alxgmpr/chipshouter-picoemp/docs/superpowers/plans/2026-07-25-picoemp-rev2026.md

# PicoEMP Rev-2026 Implementation Plan

> **For agentic workers:** REQUIRED SUB-SKILL: Use superpowers:subagent-driven-development (recommended) or superpowers:executing-plans to implement this plan task-by-task. Steps use checkbox (`- [ ]`) syntax for tracking.

**Goal:** Turn the broken in-progress KiCad port into a correct, DRC-clean, 2026-sourceable PicoEMP revision with a hand-buildable DigiKey BOM.

**Architecture:** Copy the existing schematic (whose connectivity is verified correct against the firmware pin map) into a fresh `hardware/rev2026/` project, then repair it in place — symbols, footprints, fields — under a pytest harness that asserts each invariant. Board is re-laid from scratch, replicating the hi-pot-validated HV geometry. Every gate is enforced by `kicad-cli` headlessly.

**Tech Stack:** KiCad 10.0.5 (`kicad-cli` at `/Applications/KiCad/KiCad.app/Contents/MacOS/kicad-cli`), Python 3 via `uv run --with pytest pytest`, the `kicad-happy` plugin skills, git.

**Spec:** `docs/superpowers/specs/2026-07-25-picoemp-rev2026-design.md`

## Tooling — kicad-happy skills

Use these rather than hand-rolling equivalents. Invoke via the Skill tool.

| Skill | Used in | For |
|---|---|---|
| `kicad-happy:bom` | Tasks 2, 3, 12 | `edit_properties.py` to write symbol fields; `bom_manager.py analyze` as a gap gate; `export`/`order` to generate the DigiKey order file |
| `kicad-happy:datasheets` | Tasks 2, 6 | Extract land-pattern and package specs per MPN, cached per project |
| `kicad-happy:lcsc` | Task 2 | Datasheet sync — **the only genuinely no-auth source**. Use this first |
| `kicad-happy:element14` | Task 2 | Datasheet sync — needs a **free** API key (`ELEMENT14_API_KEY`) from partner.element14.com. Simple query-param auth, no OAuth. Best PDF coverage once configured |
| `kicad-happy:digikey` | Task 2, 12 | Part validation and stock. **Requires OAuth setup — see below** |
| `kicad-happy:jlcpcb` | Task 11 | Bare-PCB fab rules and capability limits |
| `kicad-happy:kicad` | Task 13 | Full design review before ordering |

**DigiKey credentials are not configured on this machine** (`DIGIKEY_CLIENT_ID` unset, no `~/.config/secrets.env`). The DigiKey API scripts will fail until the user registers a client-credentials app at developer.digikey.com and exports `DIGIKEY_CLIENT_ID` / `DIGIKEY_CLIENT_SECRET`. **Every DigiKey step below has a no-auth fallback** (element14 or LCSC) so the plan is not blocked on it. Do not stop to ask — use the fallback and note it.

**Known tool limits — verified during execution:**
- `edit_properties.py` **sets and adds** properties; it does not delete them. Field removal uses the Task 1 parser's `property_span()` for a structural rewrite.
- **The datasheet sync scripts do NOT accept `--recursive`.** Valid flags are `--output/-o`, `--force`, `--force-all`, `--delay`, `--parallel`, `--dry-run`, `--json`, and `--mpn-list FILE`. Only `bom_manager.py` and `sync_datasheet_urls.py` take `--recursive`.
- Both sync scripts accept **`--mpn-list FILE`** (one MPN per line). For a design whose schematic MPNs are incomplete, feeding an explicit MPN list is more reliable than parsing the schematic.
- The `jlcpcb` skill does not document minimum routed slot width. Task 11 must check JLCPCB's live capability page.

## Global Constraints

- **Branch:** all work on `rev2026`. Never commit to `main`.
- **Python:** always `uv run --with pytest pytest`. Never raw `pip` or `python -m venv`.
- **Frozen values — never change:** charge PWM 2500 Hz at 1.22% duty; 5 µs default pulse; R3/R7 = 10 Ω; R9 = 2 k; D7 = 18 V ±2%; Pico pin assignment (GP0 trigger, GP6/7/27 LEDs, GP11/GP28 buttons, GP14 HVPULSE, GP18+GP26 CHARGED, GP20 HVPWM).
- **Board:** 2-layer, **1.6 mm thickness**, outline 40 × 116 mm.
- **Designators:** upstream scheme — `D6/D8/D9` LEDs, `P1/P2/P3` headers, `J1` = SMA, `J2` = JST, `J3` = HV tap. New parts: `U2, R14, R15, R16, C6, J4`.
- **Licence:** derivative of CC BY-SA 3.0 work. Attribute NewAE Technology.
- **`kicad-cli` alias:** every command below assumes `KC=/Applications/KiCad/KiCad.app/Contents/MacOS/kicad-cli`.

## ⚠️ Tasks 10 and 11 are human tasks

PCB layout is interactive GUI work. An agent cannot place or route a board. Tasks 10 and 11 must be done by a person in KiCad's PCB editor; the plan supplies the acceptance criteria and the scripted gates that verify the result, not the routing itself. Every other task is fully automatable.

## File Structure

| Path | Responsibility |
|---|---|
| `hardware/rev2026/picoemp-rev2026.kicad_pro` | Project file: netclasses, DRC rules, ERC severities |
| `hardware/rev2026/picoemp-rev2026.kicad_sch` | Schematic (seeded from the kc/ port) |
| `hardware/rev2026/picoemp-rev2026.kicad_pcb` | Board — re-laid from scratch |
| `hardware/rev2026/sym-lib-table` | Project-local symbol libraries |
| `hardware/rev2026/fp-lib-table` | Project-local footprint libraries |
| `hardware/rev2026/lib/picoemp.kicad_sym` | Custom symbols: IGBT-with-diode, LDA111 |
| `hardware/rev2026/lib/picoemp.pretty/` | Custom footprints: ATB322524, LDA111 SOP-6 |
| `hardware/rev2026/tests/kicad_parse.py` | S-expression parser + accessors (shared) |
| `hardware/rev2026/tests/test_schematic.py` | Schematic invariants |
| `hardware/rev2026/tests/test_libraries.py` | Library resolution + custom footprint geometry |
| `hardware/rev2026/tests/test_board.py` | Board setup, netclass, DRC config |
| `hardware/rev2026/tests/conftest.py` | Shared fixtures (paths, parsed docs) |
| `hardware/rev2026/out/` | Generated fab outputs (gitignored) |

`hardware/altium_src/kc/` is left untouched as the as-received reference.

---

### Task 1: Scaffold project and test harness

**Files:**
- Create: `hardware/rev2026/picoemp-rev2026.kicad_sch` (copy)
- Create: `hardware/rev2026/picoemp-rev2026.kicad_pro` (copy)
- Create: `hardware/rev2026/tests/kicad_parse.py`
- Create: `hardware/rev2026/tests/conftest.py`
- Create: `hardware/rev2026/tests/test_schematic.py`

**Interfaces:**
- Consumes: nothing.
- Produces: `kicad_parse.parse_file(path) -> list`, `kicad_parse.symbols(tree) -> list[Symbol]` where `Symbol` is a dataclass with fields `ref: str`, `value: str`, `lib_id: str`, `footprint: str`, `props: dict[str,str]`, `in_bom: bool`, `dnp: bool`. Also `kicad_parse.footprints(tree) -> list[Footprint]` with `ref: str`, `lib_id: str`, `value: str`, `pads: list[tuple[str,float,float]]`. conftest exposes fixtures `sch` (parsed schematic tree) and `syms` (list of Symbol, power symbols excluded).

- [ ] **Step 1: Create the directory and copy the source schematic**

```bash
cd /Users/alex/Downloads/chipshouter-picoemp-main
mkdir -p hardware/rev2026/tests hardware/rev2026/lib/picoemp.pretty hardware/rev2026/out
cp hardware/altium_src/kc/ChipShouter-Pico.kicad_sch hardware/rev2026/picoemp-rev2026.kicad_sch
cp hardware/altium_src/kc/ChipShouter-Pico.kicad_pro hardware/rev2026/picoemp-rev2026.kicad_pro
echo "out/" > hardware/rev2026/.gitignore
```

- [ ] **Step 2: Write the parser**

Create `hardware/rev2026/tests/kicad_parse.py`:

```python
"""Minimal KiCad s-expression parser and accessors for design-rule tests."""
import re
from dataclasses import dataclass, field

def _tokens(s):
    i, n = 0, len(s)
    while i < n:
        c = s[i]
        if c == '"':
            j, buf = i + 1, []
            while j < n:
                if s[j] == '\\':
                    buf.append(s[j + 1]); j += 2; continue
                if s[j] == '"':
                    break
                buf.append(s[j]); j += 1
            yield ('str', ''.join(buf)); i = j + 1
        elif c in '()':
            yield ('paren', c); i += 1
        elif c.isspace():
            i += 1
        else:
            j = i
            while j < n and not s[j].isspace() and s[j] not in '()"':
                j += 1
            yield ('sym', s[i:j]); i = j

def parse(text):
    """Parse s-expression text. Quoted strings become ('S', value) tuples."""
    stack = [[]]
    for kind, val in _tokens(text):
        if kind == 'paren':
            if val == '(':
                stack.append([])
            else:
                node = stack.pop()
                stack[-1].append(node)
        elif kind == 'sym':
            stack[-1].append(val)
        else:
            stack[-1].append(('S', val))
    return stack[0]

def parse_file(path):
    return parse(open(path, encoding='utf-8').read())[0]

def sval(x):
    """Unwrap a quoted-string node, else None."""
    return x[1] if isinstance(x, tuple) and x and x[0] == 'S' else None

def _walk(node, name):
    """Yield every sub-list whose head is `name`, at any depth."""
    if isinstance(node, list):
        if node and node[0] == name:
            yield node
        for child in node:
            yield from _walk(child, name)

@dataclass
class Symbol:
    ref: str = ''
    value: str = ''
    lib_id: str = ''
    footprint: str = ''
    props: dict = field(default_factory=dict)
    in_bom: bool = True
    dnp: bool = False

@dataclass
class Footprint:
    ref: str = ''
    lib_id: str = ''
    value: str = ''
    pads: list = field(default_factory=list)

def symbols(tree, include_power=False):
    out = []
    for node in tree:
        if not (isinstance(node, list) and node and node[0] == 'symbol'):
            continue
        s = Symbol()
        for e in node:
            if not isinstance(e, list) or not e:
                continue
            if e[0] == 'lib_id':
                s.lib_id = sval(e[1]) or ''
            elif e[0] == 'property':
                s.props[sval(e[1])] = sval(e[2])
            elif e[0] == 'in_bom':
                s.in_bom = (e[1] == 'yes')
            elif e[0] == 'dnp':
                s.dnp = (e[1] == 'yes')
        s.ref = s.props.get('Reference', '')
        s.value = s.props.get('Value', '')
        s.footprint = s.props.get('Footprint', '') or ''
        if s.ref.startswith('#') and not include_power:
            continue
        out.append(s)
    return out

def footprints(tree):
    out = []
    for node in _walk(tree, 'footprint'):
        f = Footprint(lib_id=sval(node[1]) or '')
        for e in node:
            if isinstance(e, list) and e and e[0] == 'property':
                if sval(e[1]) == 'Reference':
                    f.ref = sval(e[2]) or ''
                elif sval(e[1]) == 'Value':
                    f.value = sval(e[2]) or ''
        for pad in _walk(node, 'pad'):
            num = sval(pad[1]) or ''
            at = next((c for c in pad if isinstance(c, list) and c and c[0] == 'at'), None)
            if at:
                f.pads.append((num, float(at[1]), float(at[2])))
        out.append(f)
    return out

def ref_key(ref):
    """Sort key: ('R', 9) for 'R9'. Lets R9 sort before R10."""
    m = re.match(r'([A-Za-z]+)(\d+)', ref)
    return (m.group(1), int(m.group(2))) if m else (ref, 0)
```

- [ ] **Step 3: Write conftest fixtures**

Create `hardware/rev2026/tests/conftest.py`:

```python
import pathlib
import sys

import pytest

sys.path.insert(0, str(pathlib.Path(__file__).parent))
import kicad_parse as kp

ROOT = pathlib.Path(__file__).resolve().parents[1]
SCH = ROOT / 'picoemp-rev2026.kicad_sch'
PCB = ROOT / 'picoemp-rev2026.kicad_pcb'
PRO = ROOT / 'picoemp-rev2026.kicad_pro'

@pytest.fixture(scope='session')
def root():
    return ROOT

@pytest.fixture(scope='session')
def sch():
    return kp.parse_file(SCH)

@pytest.fixture(scope='session')
def syms(sch):
    return kp.symbols(sch)
```

- [ ] **Step 4: Write the characterization test**

This asserts the *current* state so we notice unintended drift. Create `hardware/rev2026/tests/test_schematic.py`:

```python
import kicad_parse as kp

# Every non-power reference expected in the design, post-rework.
EXPECTED_REFS = {
    'C1', 'C2', 'C3', 'C5', 'C6',
    'D1', 'D2', 'D3', 'D4', 'D5', 'D6', 'D7', 'D8', 'D9',
    'FID1', 'FID2', 'FID3',
    'J1', 'J2', 'J3', 'J4',
    'MH1', 'MH2', 'MH3',
    'P1', 'P2', 'P3',
    'Q1', 'Q2', 'Q3', 'Q4',
    'R1', 'R2', 'R3', 'R4', 'R5', 'R6', 'R7', 'R9',
    'R10', 'R11', 'R12', 'R13', 'R14', 'R15', 'R16',
    'SW1', 'SW2', 'SW3',
    'T1', 'T2',
    'U1', 'U2',
}

def test_parser_finds_symbols(syms):
    """Sanity: the parser reads a plausible number of components."""
    assert len(syms) > 30

def test_every_symbol_has_a_reference(syms):
    assert all(s.ref for s in syms)

def test_no_duplicate_references(syms):
    refs = [s.ref for s in syms]
    dupes = {r for r in refs if refs.count(r) > 1}
    assert not dupes, f'duplicate refs: {sorted(dupes)}'
```

- [ ] **Step 5: Run the tests — they must pass**

```bash
cd hardware/rev2026 && uv run --with pytest pytest tests/ -v
```

Expected: 3 passed. If `test_no_duplicate_references` fails, stop — the source schematic has a problem the audit did not find.

- [ ] **Step 6: Commit**

```bash
cd /Users/alex/Downloads/chipshouter-picoemp-main
git add hardware/rev2026
git commit -m "Scaffold rev2026 project and pytest design-rule harness"
```

---

### Task 2: Project-local library tables and datasheet sync

**Files:**
- Create: `hardware/rev2026/sym-lib-table`
- Create: `hardware/rev2026/fp-lib-table`
- Create: `hardware/rev2026/lib/picoemp.kicad_sym` (empty shell)
- Create: `hardware/rev2026/tests/test_libraries.py`
- Create: `hardware/datasheets/` (shared across revisions; gitignored)

**Interfaces:**
- Consumes: `kicad_parse` from Task 1.
- Produces: `${KIPRJMOD}/lib/picoemp.kicad_sym` registered as symbol lib `picoemp`; `${KIPRJMOD}/lib/picoemp.pretty` registered as footprint lib `picoemp`. Later tasks reference symbols as `picoemp:<name>` and footprints as `picoemp:<name>`. Also `hardware/datasheets/manifest.json` mapping MPN → local PDF, consumed by Task 6.

- [ ] **Step 1: Write the failing test**

Create `hardware/rev2026/tests/test_libraries.py`:

```python
import kicad_parse as kp

def test_sym_lib_table_exists_and_registers_picoemp(root):
    path = root / 'sym-lib-table'
    assert path.exists(), 'project-local sym-lib-table missing'
    text = path.read_text()
    assert 'picoemp' in text
    assert '${KIPRJMOD}/lib/picoemp.kicad_sym' in text

def test_fp_lib_table_exists_and_registers_picoemp(root):
    path = root / 'fp-lib-table'
    assert path.exists(), 'project-local fp-lib-table missing'
    text = path.read_text()
    assert 'picoemp' in text
    assert '${KIPRJMOD}/lib/picoemp.pretty' in text
```

- [ ] **Step 2: Run to verify it fails**

```bash
cd hardware/rev2026 && uv run --with pytest pytest tests/test_libraries.py -v
```

Expected: 2 failed, "project-local sym-lib-table missing".

- [ ] **Step 3: Create the library tables**

`hardware/rev2026/sym-lib-table`:

```
(sym_lib_table
  (version 7)
  (lib (name "picoemp")(type "KiCad")(uri "${KIPRJMOD}/lib/picoemp.kicad_sym")(options "")(descr "PicoEMP Rev-2026 project symbols"))
)
```

`hardware/rev2026/fp-lib-table`:

```
(fp_lib_table
  (version 7)
  (lib (name "picoemp")(type "KiCad")(uri "${KIPRJMOD}/lib/picoemp.pretty")(options "")(descr "PicoEMP Rev-2026 project footprints"))
)
```

`hardware/rev2026/lib/picoemp.kicad_sym`:

```
(kicad_symbol_lib
  (version 20241209)
  (generator "kicad_symbol_editor")
  (generator_version "10.0")
)
```

- [ ] **Step 4: Run to verify it passes**

```bash
cd hardware/rev2026 && uv run --with pytest pytest tests/test_libraries.py -v
```

Expected: 2 passed.

- [ ] **Step 5: Sync datasheets**

Invoke the `kicad-happy:element14` skill (no auth needed) and run its sync script
against the schematic. Datasheets are essential context for Task 6's footprint
work and for resolving the D7 package question in spec §10.

```bash
SK=/Users/alex/.claude/plugins/cache/kicad-happy/kicad-happy/2.0.0/skills
uv run python $SK/lcsc/scripts/sync_datasheets_lcsc.py \
  hardware/rev2026/picoemp-rev2026.kicad_sch
```

If element14 misses parts, fall back to the `kicad-happy:lcsc` sync — it shares
the same `datasheets/` directory and skips what is already downloaded:

```bash
uv run python $SK/element14/scripts/sync_datasheets_element14.py \
  hardware/rev2026/picoemp-rev2026.kicad_sch   # needs ELEMENT14_API_KEY
```

Do **not** block on DigiKey — its credentials are not configured. If the user
sets them up later, `sync_datasheets_digikey.py` gives the best coverage.

Note the schematic's MPN fields are not normalized until Task 3, so coverage will
be partial here. Re-run this step after Task 3; the scripts are idempotent.

- [ ] **Step 6: Add datasheets to gitignore**

```bash
cd /Users/alex/Downloads/chipshouter-picoemp-main
grep -q '^datasheets/' .gitignore || echo 'datasheets/' >> .gitignore
```

- [ ] **Step 7: Commit**

```bash
git add hardware/rev2026 .gitignore
git commit -m "Add project-local library tables, sync component datasheets"
```

---

### Task 3: Flatten values and normalize BOM fields

Fixes three audit findings at once: `${ALTIUM_VALUE}` indirection, C5's missing value, and the R9 part-number bug.

**Files:**
- Modify: `hardware/rev2026/picoemp-rev2026.kicad_sch`
- Modify: `hardware/rev2026/tests/test_schematic.py`

**Interfaces:**
- Consumes: `Symbol.props` from Task 1.
- Produces: every BOM symbol carries canonical fields `MPN`, `Manufacturer`, `DigiKey`, `Datasheet`. No symbol carries `PART NUMBER`, `ALTIUM_VALUE`, or Altium metadata.

- [ ] **Step 1: Write the failing tests**

Append to `hardware/rev2026/tests/test_schematic.py`:

```python
ALTIUM_CRUFT = {
    'PART NUMBER', 'ALTIUM_VALUE', 'COMPONENT GROUP', 'COMPONENT KIND',
    'COMPONENT TYPE', 'PIN COUNT', 'PP MATERIAL STACK', 'PP ROTATION',
    'PP ROTATION1', 'MOUNTING TECHNOLOGY', 'LATESTREVISIONDATE',
    'LATESTREVISIONNOTE', 'PUBLISHER', 'SNAPEDA_LINK', 'CHECK_PRICES',
    'AVAILABILITY', 'PRICE', 'MANUFACTURE 1', 'MANUFACTURE PART NUMBER 1',
    'SUPPLIER 1', 'SUPPLIER PART NUMBER 1', 'MANUFACTURER_NAME',
    'MANUFACTURER_PART_NUMBER', 'MOUSER PART NUMBER', 'MOUSER PRICE/STOCK',
    'ARROW PART NUMBER', 'ARROW PRICE/STOCK', 'DATASHEET LINK', 'ROHS',
    'CASE-EIA', 'CASE-METRIC', 'RATED POWER', 'RATED VOLTAGE', 'TOLERANCE',
    'TEMPERATURE RANGE', 'HEIGHT', 'PACKAGE', 'PURCHASE-URL', 'MP', 'MF',
}

def test_no_unresolved_value_variables(syms):
    bad = [s.ref for s in syms if '${' in s.value]
    assert not bad, f'symbols with unresolved value variables: {bad}'

def test_c5_has_its_value(syms):
    c5 = next(s for s in syms if s.ref == 'C5')
    assert c5.value == '100n'

def test_no_altium_cruft_fields(syms):
    offenders = {s.ref: sorted(set(s.props) & ALTIUM_CRUFT)
                 for s in syms if set(s.props) & ALTIUM_CRUFT}
    assert not offenders, f'Altium metadata remains: {offenders}'

def test_r9_part_data_is_2k_not_75r():
    """Upstream bug: R9 carried R4's part data throughout."""
    import conftest
    syms = kp.symbols(kp.parse_file(conftest.SCH))
    r9 = next(s for s in syms if s.ref == 'R9')
    assert r9.value == '2k'
    assert r9.props.get('MPN') == 'RC0805FR-072KL'
    assert r9.props.get('DigiKey') == '311-2.00KCRCT-ND'
```

- [ ] **Step 2: Run to verify they fail**

```bash
cd hardware/rev2026 && uv run --with pytest pytest tests/test_schematic.py -v
```

Expected: 4 failed — unresolved `${ALTIUM_VALUE}` on 11 symbols, C5 value wrong, cruft present, R9 has no `MPN`.

- [ ] **Step 3: Write the field-rewrite script**

Create `hardware/rev2026/tools/normalize_fields.py`:

```python
"""One-shot: flatten ${ALTIUM_VALUE}, rename fields to canonical names,
strip Altium metadata. Operates on the schematic text directly to preserve
formatting and UUIDs."""
import pathlib
import re
import sys

sys.path.insert(0, str(pathlib.Path(__file__).resolve().parents[1] / 'tests'))
import kicad_parse as kp

SCH = pathlib.Path(__file__).resolve().parents[1] / 'picoemp-rev2026.kicad_sch'

RENAME = {
    'MANUFACTURE PART NUMBER 1': 'MPN',
    'MANUFACTURER_PART_NUMBER': 'MPN',
    'MANUFACTURE 1': 'Manufacturer',
    'MANUFACTURER_NAME': 'Manufacturer',
    'SUPPLIER PART NUMBER 1': 'DigiKey',
}

DROP = {
    'PART NUMBER', 'COMPONENT GROUP', 'COMPONENT KIND', 'COMPONENT TYPE',
    'PIN COUNT', 'PP MATERIAL STACK', 'PP ROTATION', 'PP ROTATION1',
    'MOUNTING TECHNOLOGY', 'LATESTREVISIONDATE', 'LATESTREVISIONNOTE',
    'PUBLISHER', 'SNAPEDA_LINK', 'CHECK_PRICES', 'AVAILABILITY', 'PRICE',
    'SUPPLIER 1', 'MOUSER PART NUMBER', 'MOUSER PRICE/STOCK',
    'ARROW PART NUMBER', 'ARROW PRICE/STOCK', 'ROHS', 'CASE-EIA',
    'CASE-METRIC', 'RATED POWER', 'RATED VOLTAGE', 'TOLERANCE',
    'TEMPERATURE RANGE', 'HEIGHT', 'PACKAGE', 'PURCHASE-URL', 'MP', 'MF',
    'DATASHEET LINK',
}

def main():
    text = SCH.read_text(encoding='utf-8')

    # 1. Flatten ${ALTIUM_VALUE} using each symbol's own ALTIUM_VALUE property.
    #    Symbol blocks start at a tab-tab (lib_id line; split on those boundaries.
    starts = [m.start() for m in re.finditer(r'\n\t\t\(lib_id "', text)]
    starts.append(len(text))
    out = [text[:starts[0]]] if starts else [text]
    for a, b in zip(starts, starts[1:]):
        blk = text[a:b]
        av = re.search(r'\(property "ALTIUM_VALUE"\s+"([^"]*)"', blk)
        if av and '${ALTIUM_VALUE}' in blk:
            blk = blk.replace('${ALTIUM_VALUE}', av.group(1))
        out.append(blk)
    text = ''.join(out)

    # 2. Rename fields.
    for old, new in RENAME.items():
        text = text.replace(f'(property "{old}"', f'(property "{new}"')

    # 3. Drop unwanted property blocks (single-level, tab-tab-tab indented).
    for name in DROP | {'ALTIUM_VALUE'}:
        pattern = re.compile(
            r'\n\t\t\t\(property "' + re.escape(name) + r'"(?:[^()]|\((?:[^()]|\([^()]*\))*\))*\)',
            re.S)
        text = pattern.sub('', text)

    SCH.write_text(text, encoding='utf-8')
    print('normalized')

if __name__ == '__main__':
    main()
```

- [ ] **Step 4: Run the deletion/flatten script**

This handles only flattening, renaming and removal — `edit_properties.py` cannot
delete properties.

```bash
cd hardware/rev2026 && uv run python tools/normalize_fields.py
```

- [ ] **Step 5: Set the corrected values with the bom skill**

Invoke `kicad-happy:bom`, then use its `edit_properties.py` rather than clicking
through the GUI. KiCad must be closed, or the changes will be overwritten by its
in-memory copy.

```bash
SK=/Users/alex/.claude/plugins/cache/kicad-happy/kicad-happy/2.0.0/skills
cd /Users/alex/Downloads/chipshouter-picoemp-main
cat > /tmp/updates.json <<'EOF'
{
  "C5": {"Value": "100n", "MPN": "C0603C104K5RACTU", "Manufacturer": "KEMET",
         "DigiKey": "399-5089-2-ND"},
  "R9": {"Value": "2k", "MPN": "RC0805FR-072KL", "Manufacturer": "Yageo",
         "DigiKey": "311-2.00KCRCT-ND"}
}
EOF
uv run python $SK/bom/scripts/edit_properties.py \
  hardware/rev2026/picoemp-rev2026.kicad_sch --updates /tmp/updates.json --dry-run
```

Review the dry-run diff, then re-run without `--dry-run`.

- [ ] **Step 6: Backfill the remaining MPN and DigiKey fields**

Build the rest of `/tmp/updates.json` from spec §5.2 and §5.3 and apply it the same
way. Every BOM symbol needs `MPN`, `Manufacturer` and `DigiKey`. Use the DigiKey
part numbers already recorded in the spec — they came from upstream's published
BOM and were verified Active during the audit.

- [ ] **Step 7: Gate on the bom skill's gap report**

```bash
uv run python $SK/bom/scripts/bom_manager.py analyze \
  hardware/rev2026/picoemp-rev2026.kicad_sch --json --recursive \
  | python3 -c "import json,sys; d=json.load(sys.stdin); \
print('without_mpn:', d['stats']['without_mpn']); \
print(json.dumps(d['convention']['field_mapping'], indent=1))"
```

Expected: `without_mpn: 0`, and the field mapping resolves `mpn` → `MPN`,
`manufacturer` → `Manufacturer`. If the analyzer still reports `PART NUMBER` as
the MPN field, the deletion step did not take.

- [ ] **Step 8: Run tests to verify they pass**

```bash
cd hardware/rev2026 && uv run --with pytest pytest tests/test_schematic.py -v
```

Expected: all passed.

- [ ] **Step 9: Re-run the datasheet sync**

Now that MPNs are populated, coverage will be much better. Idempotent.

```bash
uv run python $SK/lcsc/scripts/sync_datasheets_lcsc.py \
  hardware/rev2026/picoemp-rev2026.kicad_sch
uv run python $SK/bom/scripts/sync_datasheet_urls.py \
  hardware/rev2026/picoemp-rev2026.kicad_sch --recursive --dry-run
```

Review, then re-run the URL backfill without `--dry-run` to populate empty
`Datasheet` fields from the manifest.

- [ ] **Step 10: Commit**

```bash
git add hardware/rev2026
git commit -m "Flatten Altium value variables, normalize BOM fields, fix R9 part data

R9's value is 2k but every part field carried R4's 75R data
(RCHIP-75R-0805 / RC0805FR-0775RL / 311-75.0CRCT-ND). This is an
upstream defect in the Altium source; the published .xls BOM has the
correct RC0805FR-072KL. design_notes confirms 2k is the validated
gate-drive shunt."
```

---

### Task 4: Custom symbols — IGBT with antiparallel diode, LDA111

**Files:**
- Modify: `hardware/rev2026/lib/picoemp.kicad_sym`
- Modify: `hardware/rev2026/tests/test_libraries.py`

**Interfaces:**
- Consumes: `picoemp` symbol lib from Task 2.
- Produces: symbols `picoemp:IGBT_NCH_Diode` (3 pins: 1=G, 2=C, 3=E) and `picoemp:LDA111` (6 pins: 1=A, 2=K, 4=E, 5=C, 6=B; pin 3 absent). Task 5 assigns these.

- [ ] **Step 1: Write the failing test**

Append to `hardware/rev2026/tests/test_libraries.py`:

```python
def _lib_symbol_names(root):
    text = (root / 'lib' / 'picoemp.kicad_sym').read_text()
    return set(re.findall(r'\n\t\(symbol "([^"]+)"', text))

def test_custom_symbols_exist(root):
    names = _lib_symbol_names(root)
    assert 'IGBT_NCH_Diode' in names, 'IGBT symbol with antiparallel diode missing'
    assert 'LDA111' in names, 'LDA111 Darlington opto symbol missing'

def test_igbt_pin_names(root):
    """DPAK IGBT: pin 1 Gate, pin 2 Collector, pin 3 Emitter."""
    text = (root / 'lib' / 'picoemp.kicad_sym').read_text()
    body = text.split('(symbol "IGBT_NCH_Diode"')[1].split('\n\t(symbol "')[0]
    for num, name in (('1', 'G'), ('2', 'C'), ('3', 'E')):
        assert f'(name "{name}"' in body, f'IGBT missing pin name {name}'
        assert f'(number "{num}"' in body, f'IGBT missing pin number {num}'

def test_lda111_pin_numbers(root):
    """6-pin opto, pin 3 is absent (NC)."""
    text = (root / 'lib' / 'picoemp.kicad_sym').read_text()
    body = text.split('(symbol "LDA111"')[1].split('\n\t(symbol "')[0]
    nums = set(re.findall(r'\(number "(\d)"', body))
    assert nums == {'1', '2', '4', '5', '6'}, f'unexpected LDA111 pins: {sorted(nums)}'
```

Add `import re` at the top of the file.

- [ ] **Step 2: Run to verify it fails**

```bash
cd hardware/rev2026 && uv run --with pytest pytest tests/test_libraries.py -v
```

Expected: 3 failed, "IGBT symbol with antiparallel diode missing".

- [ ] **Step 3: Author the two symbols**

Either draw them in KiCad's Symbol Editor, or author the `.kicad_sym`
s-expressions directly — the file format is plain text and the tests below
validate structure either way. Authoring directly is usually faster and is
fully scriptable.

Whichever route, both symbols must pass the validation in Step 3b.

**`IGBT_NCH_Diode`** — start from `Device:Q_NIGBT_GCE`, then add a diode from collector to emitter (cathode at collector) to represent the co-packed antiparallel diode. Pins: `1` = `G` (input), `2` = `C` (passive), `3` = `E` (passive). Set `Value` = `RGT16BM65DTL`, `Footprint` = `Package_TO_SOT_SMD:TO-252-3_TabPin2`, `Datasheet` = `https://fscdn.rohm.com/en/products/databook/datasheet/discrete/igbt/rgt16bm65d-e.pdf`.

**`LDA111`** — an LED (pins 1 anode / 2 cathode) optically coupled to a Darlington pair with the base brought out. Pins: `1` = `A`, `2` = `K`, `4` = `E`, `5` = `C`, `6` = `B`. **No pin 3** — it is a no-connect on the physical part. Set `Value` = `LDA111STR`, `Footprint` = `picoemp:SOP-6_LDA111`, `Datasheet` = `https://www.littelfuse.com/products/power-semiconductors-control-ics/integrated-circuits/optocouplers/single-optocouplers/lda111`.

- [ ] **Step 3b: Validate that KiCad can actually load and render both symbols**

Structural tests prove the pins are right; these prove KiCad accepts the file.

```bash
KC=/Applications/KiCad/KiCad.app/Contents/MacOS/kicad-cli
cd /Users/alex/Downloads/chipshouter-picoemp-main/hardware/rev2026

# Parse gate: non-zero exit or an error means the library is malformed.
"$KC" sym upgrade --force -o /tmp/picoemp-upgraded.kicad_sym lib/picoemp.kicad_sym

# Render gate: KiCad must be able to draw both symbols.
mkdir -p /tmp/symsvg && "$KC" sym export svg -o /tmp/symsvg lib/picoemp.kicad_sym
ls /tmp/symsvg
```

Expected: `sym upgrade` exits 0, and `/tmp/symsvg` contains an SVG per symbol.
An empty output directory means KiCad silently rejected the symbol — treat that
as a failure even if `sym upgrade` passed.

- [ ] **Step 4: Run to verify it passes**

```bash
cd hardware/rev2026 && uv run --with pytest pytest tests/test_libraries.py -v
```

Expected: all passed.

- [ ] **Step 5: Commit**

```bash
git add hardware/rev2026/lib hardware/rev2026/tests
git commit -m "Add custom symbols: IGBT with antiparallel diode, LDA111 Darlington opto"
```

---

### Task 5: Correct all symbol assignments

**Files:**
- Modify: `hardware/rev2026/picoemp-rev2026.kicad_sch`
- Modify: `hardware/rev2026/tests/test_schematic.py`

**Interfaces:**
- Consumes: `picoemp:IGBT_NCH_Diode`, `picoemp:LDA111` from Task 4.
- Produces: no symbol uses a depletion-MOSFET, Schottky, or unresolvable `lib_id`.

- [ ] **Step 1: Write the failing tests**

Append to `hardware/rev2026/tests/test_schematic.py`:

```python
def test_no_wildcard_or_altium_lib_ids(syms):
    bad = [(s.ref, s.lib_id) for s in syms
           if '*' in s.lib_id or 'AltiumLib' in s.lib_id or 'DBLib' in s.lib_id]
    assert not bad, f'unresolvable lib_ids: {bad}'

def test_mosfets_are_enhancement_not_depletion(syms):
    bad = [s.ref for s in syms if 'Depletion' in s.lib_id]
    assert not bad, f'depletion-mode symbol used for enhancement parts: {bad}'

def test_igbt_uses_igbt_symbol(syms):
    q2 = next(s for s in syms if s.ref == 'Q2')
    assert q2.lib_id == 'picoemp:IGBT_NCH_Diode'

def test_rectifiers_are_not_schottky(syms):
    """Upstream errata: D1/D3/D4/D5 were never Schottky diodes."""
    for ref in ('D1', 'D3', 'D4', 'D5'):
        s = next(x for x in syms if x.ref == ref)
        assert 'Schottky' not in s.lib_id, f'{ref} still drawn as Schottky'

def test_opto_uses_custom_symbol(syms):
    q1 = next(s for s in syms if s.ref == 'Q1')
    assert q1.lib_id == 'picoemp:LDA111'

def test_transformers_use_project_symbol(syms):
    for ref in ('T1', 'T2'):
        s = next(x for x in syms if x.ref == ref)
        assert s.lib_id == 'picoemp:ATB322524'

def test_mosfets_use_numeric_pin_symbol(syms):
    """SOT-23 pads are 1/2/3, so the symbol's pins must be too."""
    for ref in ('Q3', 'Q4'):
        s = next(x for x in syms if x.ref == ref)
        assert s.lib_id == 'Transistor_FET:Q_NMOS_GSD'
```

- [ ] **Step 2: Run to verify they fail**

```bash
cd hardware/rev2026 && uv run --with pytest pytest tests/test_schematic.py -v
```

Expected: 6 failed.

- [ ] **Step 3: Create the `picoemp:ATB322524` transformer symbol**

`Device:Transformer_1P_1S` groups pins 1,2 as primary and 3,4 as secondary.
**This design is wired primary = 1,4 and secondary = 2,3** — verified from the
netlist: T1 pin 1 → Q3 drain, pin 4 → C1 (primary); pin 2 → D2 anode, pin 3 →
D7 anode (secondary). T2 follows the same grouping.

Add `ATB322524` to `lib/picoemp.kicad_sym`: two windings, primary on pins 1 and
4, secondary on pins 2 and 3, all `passive`. `Reference` prefix `T`, `Value`
`ATB322524-0110-T000`. Place the polarity dot to match the existing Altium
symbol's graphics and `hardware/BUILD-DRAWING-REV04.PDF` — upstream flags
transformer orientation as a build hazard, and reversing it produced the
wrong-polarity spike on the original prototype.

Validate with the same gates Task 4 used: `kicad-cli sym upgrade --force` must
exit 0 and `sym export svg` must render it.

- [ ] **Step 4: Swap the symbols**

| Ref | New `lib_id` | Pin numbers change? |
|---|---|---|
| Q2 | `picoemp:IGBT_NCH_Diode` | **yes** — `D`,`G`,`S` → `1`,`2`,`3` |
| Q3, Q4 | `Transistor_FET:Q_NMOS_GSD` | **yes** — `D`,`G`,`S` → `1`,`2`,`3` |
| D1, D3, D4, D5 | `Device:D_Small` | no |
| Q1 | `picoemp:LDA111` | no (pin 3 dropped, was unconnected) |
| T1, T2 | `picoemp:ATB322524` | no |

**⚠️ Q2, Q3 and Q4 change pin numbering, so KiCad cannot auto-preserve their
connections.** It matches by pin number, and `D` does not map to `2`. Reconnect
these deliberately to exactly this mapping:

| Ref | Old pin | Net | New pin |
|---|---|---|---|
| Q2 | `G` | `Net-(D7-K)` | `1` (G) |
| Q2 | `D` | `Net-(J6-Ext)` | `2` (C) |
| Q2 | `S` | `Net-(D7-A)` | `3` (E) |
| Q3 | `G` | `Net-(D4-K)` | `1` (G) |
| Q3 | `S` | `GND` | `2` (S) |
| Q3 | `D` | `Net-(Q3-PadD)` | `3` (D) |
| Q4 | `G` | `Net-(D5-K)` | `1` (G) |
| Q4 | `S` | `GND` | `2` (S) |
| Q4 | `D` | `Net-(Q4-PadD)` | `3` (D) |

Getting this wrong swaps gate and collector on a 650 V IGBT. Match on the
*connection*, not the literal net-name string, in case names have drifted.

- [ ] **Step 4b: Verify the remap**

Export the netlist and confirm each transistor's pin→net mapping matches the
table above. Every other component's connectivity must be byte-identical to
before this task.

- [ ] **Step 4: Run to verify they pass**

```bash
cd hardware/rev2026 && uv run --with pytest pytest tests/test_schematic.py -v
```

Expected: all passed.

- [ ] **Step 5: Commit**

```bash
git add hardware/rev2026
git commit -m "Correct symbol classes: IGBT, enhancement MOSFETs, non-Schottky rectifiers

D1/D3/D4/D5 were drawn as Schottky diodes. This is a documented
upstream errata - hardware/README.md notes the schematic 'claimed they
were Schottky diodes, but as @settinger caught this was never the case'."
```

---

### Task 6: Custom footprints — ATB322524 and LDA111

**Files:**
- Create: `hardware/rev2026/lib/picoemp.pretty/ATB322524.kicad_mod`
- Create: `hardware/rev2026/lib/picoemp.pretty/SOP-6_LDA111.kicad_mod`
- Modify: `hardware/rev2026/tests/test_libraries.py`

**Interfaces:**
- Consumes: `picoemp` footprint lib from Task 2.
- Produces: footprints `picoemp:ATB322524` (4 pads) and `picoemp:SOP-6_LDA111` (5 pads, numbered 1,2,4,5,6). Task 7 assigns these.

- [ ] **Step 1: Write the failing test**

Append to `hardware/rev2026/tests/test_libraries.py`:

```python
import kicad_parse as kp

def _fp(root, name):
    return kp.footprints(kp.parse_file(root / 'lib' / 'picoemp.pretty' / f'{name}.kicad_mod'))[0]

def test_atb322524_footprint_geometry(root):
    """TDK ATB3225: 3.2 x 2.5 mm body, 4 pads, two per side."""
    fp = _fp(root, 'ATB322524')
    assert len(fp.pads) == 4, f'expected 4 pads, got {len(fp.pads)}'
    xs = sorted({round(x, 2) for _, x, _ in fp.pads})
    assert len(xs) == 2, f'pads should form two columns, got x positions {xs}'
    assert 2.0 <= (xs[1] - xs[0]) <= 3.2, f'pad column spacing {xs[1]-xs[0]} mm out of range'

def test_lda111_footprint_has_all_six_pads(root):
    """Pin 3 is electrically NC but the lead physically exists, so it needs a
    pad. Verified against the original SamacSys footprint in
    hardware/altium_src/kc/ChipShouter-Pico.kicad_pcb, which has 6 pads with
    pad 3 at (-4.425, 2.54). Omitting it would leave a lead unsoldered."""
    fp = _fp(root, 'SOP-6_LDA111')
    nums = {n for n, _, _ in fp.pads}
    assert nums == {'1', '2', '3', '4', '5', '6'}, f'unexpected pads: {sorted(nums)}'

def test_lda111_footprint_geometry(root):
    """SOP254P952X470-6N: 2.54 mm pitch, pad centres at x = +/-4.425
    (8.85 mm span). The 9.52 mm in the package name is lead-tip to lead-tip,
    not pad centre to pad centre."""
    fp = _fp(root, 'SOP-6_LDA111')
    ys = sorted({round(y, 2) for _, _, y in fp.pads})
    pitches = {round(b - a, 2) for a, b in zip(ys, ys[1:])}
    assert pitches == {2.54}, f'expected uniform 2.54 mm pitch, got y positions {ys}'
    xs = sorted({round(x, 2) for _, x, _ in fp.pads})
    assert len(xs) == 2, f'pads should form two rows, got x positions {xs}'
    span = xs[1] - xs[0]
    assert 8.6 <= span <= 9.1, f'pad-centre span {span} mm, expected ~8.85'
```

- [ ] **Step 2: Run to verify it fails**

```bash
cd hardware/rev2026 && uv run --with pytest pytest tests/test_libraries.py -v
```

Expected: 3 failed with `FileNotFoundError`.

- [ ] **Step 3: Extract the land patterns from the datasheets**

Invoke the `kicad-happy:datasheets` skill and extract structured package specs for
`ATB322524-0110-T000` and `LDA111STR` from the PDFs synced in Task 2. Work from
those numbers, not from memory or distributor parametrics — the audit found
distributor data wrong on package for both D7 and the SM4005PL.

If a PDF is missing from `hardware/datasheets/`, fetch the TDK ATB3225 datasheet
from `https://mm.digikey.com/Volume0/opasdata/d220001/medias/docus/644/ATB322515-(15,24)_DS.pdf`.

Record for each: body dimensions, pad size, pad pitch, row span, and the
manufacturer's recommended land pattern.

- [ ] **Step 4: Draw the footprints**

Open KiCad → Footprint Editor → `picoemp` library.

**`ATB322524`** — body 3.2 × 2.5 mm max, height 2.4 mm max. Four terminals: pins 1 and 4 on one side, 2 and 3 on the other. Use the datasheet's recommended land pattern. Add a **polarity dot marker on the silkscreen at pin 1** — upstream flags transformer orientation as a build hazard, and reversing it produced the wrong-polarity spike on the original prototype.

**`SOP-6_LDA111`** — 6-pin gull-wing, 2.54 mm pitch (SamacSys name
`SOP254P952X470-6N`, body height 4.70 mm). **Include all six pads.** Pin 3 is
electrically NC but its lead physically exists — the original SamacSys footprint
has 6 pads with pad 3 at (−4.425, 2.54), and omitting it would leave a lead
unsoldered. Pad centres sit at x = ±4.425 (8.85 mm span); the 9.52 mm in the
package name is lead-tip to lead-tip, not pad centre to pad centre.

Mark pin 1 on the silkscreen; upstream's build notes call this out specifically
as easy to get wrong.

⚠️ **Parity note for Task 11.** The `picoemp:LDA111` symbol has five pins (no
pin 3), while this footprint has six pads. Pad 3 will carry no net. If Task 11's
`pcb drc --schematic-parity` flags the unmatched pad, the fix is to restore
pin 3 to the symbol as an `unconnected`-type pin and place a no-connect flag on
it in the schematic — which is what the original Altium design did. Do not
delete the pad.

- [ ] **Step 5: Verify D7 and the rectifier lands against their datasheets**

Two spec §10 items resolve here. Using the extracted specs, confirm:

- **D7 `MM3Z18VB` is SOD-323F** (flat lead, 200 mW), not plain SOD-323. If the
  datasheet says otherwise, change the Task 7 footprint map accordingly.
- **`SM4005PL-TP` is SOD-123FL** with a ~2.36 mm land span, and KiCad's
  `Diode_SMD:D_SOD-123F` matches it within tolerance. If it does not, draw a
  `picoemp:D_SOD-123FL` and use that instead.

Record the outcome in the commit message.

- [ ] **Step 6: Run to verify it passes**

```bash
cd hardware/rev2026 && uv run --with pytest pytest tests/test_libraries.py -v
```

Expected: all passed. If the pitch assertion fails, re-measure against the datasheet rather than loosening the test.

- [ ] **Step 7: Commit**

```bash
git add hardware/rev2026/lib hardware/rev2026/tests
git commit -m "Add ATB322524 transformer and LDA111 SOP-6 footprints with pin-1 markers

Land patterns extracted from manufacturer datasheets rather than
distributor parametrics - the audit found distributor package data
wrong for both D7 (SOD-323 vs SOD-323F) and SM4005PL-TP."
```

---

### Task 7: Assign every footprint

**Files:**
- Modify: `hardware/rev2026/picoemp-rev2026.kicad_sch`
- Modify: `hardware/rev2026/tests/test_schematic.py`

**Interfaces:**
- Consumes: custom footprints from Task 6, library tables from Task 2.
- Produces: every BOM symbol has a `Lib:Name` footprint that resolves.

- [ ] **Step 1: Write the failing tests**

Append to `hardware/rev2026/tests/test_schematic.py`:

```python
FOOTPRINTS = {
    'C1': 'Capacitor_SMD:C_0805_2012Metric',
    'C2': 'Capacitor_SMD:C_0805_2012Metric',
    'C3': 'Capacitor_SMD:C_2220_5750Metric',
    'C5': 'Capacitor_SMD:C_0603_1608Metric',
    'C6': 'Capacitor_SMD:C_0603_1608Metric',
    'D1': 'picoemp:D_SOD-123FL',
    'D2': 'Diode_SMD:D_SMA',
    'D3': 'picoemp:D_SOD-123FL',
    'D4': 'picoemp:D_SOD-123FL',
    'D5': 'picoemp:D_SOD-123FL',
    'D7': 'Diode_SMD:D_SOD-323F',
    'Q1': 'picoemp:SOP-6_LDA111',
    'Q2': 'Package_TO_SOT_SMD:TO-252-3_TabPin2',
    'Q3': 'Package_TO_SOT_SMD:SOT-23',
    'Q4': 'Package_TO_SOT_SMD:SOT-23',
    'T1': 'picoemp:ATB322524',
    'T2': 'picoemp:ATB322524',
    'U1': 'Module:RaspberryPi_Pico_SMD',
    'U2': 'Package_TO_SOT_SMD:SOT-23-5',
    'J1': 'Connector_Coaxial:SMA_Amphenol_132289_EdgeMount',
    'J2': 'Connector_JST:JST_XH_S2B-XH-A_1x02_P2.50mm_Horizontal',
    'J4': 'Connector_Coaxial:SMA_Amphenol_132289_EdgeMount',
}

def test_every_symbol_has_a_footprint(syms):
    missing = [s.ref for s in syms if not s.footprint]
    assert not missing, f'symbols with no footprint: {sorted(missing, key=kp.ref_key)}'

def test_every_footprint_has_a_library_prefix(syms):
    bad = [(s.ref, s.footprint) for s in syms if ':' not in s.footprint]
    assert not bad, f'footprints with no library prefix: {bad}'

def test_no_absolute_path_footprints(syms):
    bad = [(s.ref, s.footprint) for s in syms
           if 'Users' in s.footprint or 'Documents' in s.footprint]
    assert not bad, f'absolute-path footprints: {bad}'

def test_expected_footprint_assignments(syms):
    by_ref = {s.ref: s.footprint for s in syms}
    wrong = {r: (by_ref.get(r), want) for r, want in FOOTPRINTS.items()
             if by_ref.get(r) != want}
    assert not wrong, f'footprint mismatches (got, want): {wrong}'
```

- [ ] **Step 2: Run to verify they fail**

```bash
cd hardware/rev2026 && uv run --with pytest pytest tests/test_schematic.py -v
```

Expected: 4 failed. `test_every_symbol_has_a_footprint` should list at least `D1, Q2, Q3, Q4, SW1, SW2, SW3, J3`.

- [ ] **Step 3: Assign footprints in KiCad**

Use Tools → Assign Footprints (CvPcb), or edit the Footprint field in the Symbol Fields Table. Apply the `FOOTPRINTS` map above. Resistors and LEDs follow the standard pattern:

- `R1` → `Resistor_SMD:R_2010_5025Metric`
- `R2` → `Resistor_SMD:R_2512_6332Metric`
- `R4`, `R9` → `Resistor_SMD:R_0805_2012Metric`
- `R3`, `R5`, `R6`, `R7`, `R10`–`R16` → `Resistor_SMD:R_0603_1608Metric`
- `D6`, `D8`, `D9` → `LED_SMD:LED_0603_1608Metric`
- `MH1`–`MH3` → `MountingHole:MountingHole_3.2mm_M3_Pad_Via`
- `FID1`–`FID3` → `Fiducial:Fiducial_0.5mm_Mask1.5mm`

`SW1`–`SW3`, `P1`–`P3` and `J3` are assigned in Tasks 8 and 11.

- [ ] **Step 4: Run to verify they pass**

```bash
cd hardware/rev2026 && uv run --with pytest pytest tests/test_schematic.py -k footprint -v
```

Expected: `test_every_footprint_has_a_library_prefix`, `test_no_absolute_path_footprints`, and `test_expected_footprint_assignments` pass. `test_every_symbol_has_a_footprint` still fails on `SW1/SW2/SW3/P1/P2/P3/J3` — that is correct at this stage.

- [ ] **Step 5: Commit**

```bash
git add hardware/rev2026
git commit -m "Assign resolvable footprints to all but switches, headers and J3"
```

---

### Task 8: Restore designators and fix header pitch

**Files:**
- Modify: `hardware/rev2026/picoemp-rev2026.kicad_sch`
- Modify: `hardware/rev2026/tests/test_schematic.py`

**Interfaces:**
- Consumes: Task 7's footprint assignments.
- Produces: upstream designators restored; `P1`/`P2`/`P3` on 2.54 mm footprints; `SW1`–`SW3` footprinted.

- [ ] **Step 1: Write the failing tests**

Append to `hardware/rev2026/tests/test_schematic.py`:

```python
def test_upstream_designators_restored(syms):
    refs = {s.ref for s in syms}
    assert {'D6', 'D8', 'D9'} <= refs, 'LEDs must be D6/D8/D9, not LED1-3'
    assert not (refs & {'LED1', 'LED2', 'LED3'}), 'LED1-3 designators still present'
    assert {'P1', 'P2', 'P3'} <= refs, 'headers must be P1/P2/P3'
    assert {'J1', 'J2', 'J3', 'J4'} <= refs
    assert 'J5' not in refs and 'J6' not in refs, 'stale J5/J6 designators remain'

def test_sma_is_j1(syms):
    j1 = next(s for s in syms if s.ref == 'J1')
    assert 'SMA' in j1.footprint

def test_headers_are_2540um_pitch(syms):
    """All original headers are 2.54 mm; the port had them at 1.00/1.27 mm."""
    for ref in ('P1', 'P2', 'P3'):
        s = next(x for x in syms if x.ref == ref)
        assert 'P2.54mm' in s.footprint, f'{ref} footprint {s.footprint!r} is not 2.54 mm pitch'

def test_switches_have_footprints(syms):
    for ref in ('SW1', 'SW2', 'SW3'):
        s = next(x for x in syms if x.ref == ref)
        assert s.footprint, f'{ref} has no footprint'

def test_all_expected_refs_present(syms):
    assert {s.ref for s in syms} == EXPECTED_REFS
```

- [ ] **Step 2: Run to verify they fail**

```bash
cd hardware/rev2026 && uv run --with pytest pytest tests/test_schematic.py -v
```

Expected: 5 failed.

- [ ] **Step 3: Rename and re-footprint in KiCad**

Renames (Schematic Editor, edit each Reference):

| Current | New |
|---|---|
| `LED1` | `D6` |
| `LED2` | `D8` |
| `LED3` | `D9` |
| `J1` (1×7 header) | `P1` |
| `J4` (1×2 header) | `P2` |
| `J5` (1×4 header) | `P3` |
| `J6` (SMA) | `J1` |

Then assign:

- `P1` → `Connector_PinHeader_2.54mm:PinHeader_1x07_P2.54mm_Vertical`
- `P2` → `Connector_PinHeader_2.54mm:PinHeader_1x02_P2.54mm_Vertical`
- `P3` → `Connector_PinHeader_2.54mm:PinHeader_1x04_P2.54mm_Vertical`

**Switches — spec §10 resolved: keep upstream's exact parts.** The
standardization idea came from the JLCPCB-assembly path, where `KSC741JLFS` had
only 39 units in JLC's library. This is a **DigiKey hand build**, so LCSC stock
is irrelevant and both upstream parts are Active and orderable:

| Ref | Part | Actuator | Force | DigiKey |
|---|---|---|---|---|
| SW1, SW2 | C&K `KSC741JLFS` | 4.30 mm | 390 gf | `CKN10309CT-ND` |
| SW3 | E-Switch `TL3301AF160QJ` | 5.00 mm | 160 gf | Active, 11-wk lead |

This is the combination upstream validated against the 1551B shield, so no
physical measurement is needed. The heavy 390 gf on the arm/trigger buttons and
the taller, lighter discharge button are both deliberate.

**Footprint:** use KiCad's stock **`Button_Switch_SMD:SW_Push_1P1T_NO_CK_KSC7xxJ`**
— the C&K KSC7xx J-bend land — for all three. Prefer it over the as-received
board's `CK_KSC7J` import, which is unverified.

⚠️ Upstream states SW3's TL3301A shares the KSC741J footprint ("you can use the
same PN as SW3 — the footprint is the same"), and both are J-lead. But the bodies
differ slightly (6.2 × 6.2 mm vs 6.0 × 6.0 mm). **Verify the TL3301A's J-lead pad
positions against the KSC7xxJ land from its datasheet.** If they differ
materially, give SW3 its own footprint rather than forcing the shared one.

**This task also owns the last three missing MPNs.** After Task 3, exactly three
BOM lines have no `MPN`, and no other task claims them:

| Line | Set |
|---|---|
| `D6`, `D9` (red LEDs) | **`APT1608SURCK`**, Kingbright — spec §5.1 change 1. The original `APT1608SRCPRV` is obsolete and no longer manufactured; this is DigiKey's named substitute |
| `SW1`, `SW2` | the C&K part chosen above |
| `SW3` | the C&K part chosen above |

Set `MPN`, `Manufacturer` and `DigiKey` on each using `edit_properties.py`, the
same way Task 3 did. Verify with:

```bash
uv run python "$SK/bom/scripts/bom_manager.py" analyze \
  hardware/rev2026/picoemp-rev2026.kicad_sch --gaps-only
```

Expected: no lines missing MPN.

Clear the DNP and `in_bom=no` flags on `P1`, `P2`, `P3`, `J2` and `J3` — J2 is the battery input and must appear in the BOM.

- [ ] **Step 4: Run to verify they pass**

```bash
cd hardware/rev2026 && uv run --with pytest pytest tests/test_schematic.py -v
```

Expected: all passed, including `test_all_expected_refs_present`.

- [ ] **Step 5: Commit**

```bash
git add hardware/rev2026
git commit -m "Restore upstream designators and fix header pitch to 2.54mm

The port had P1/P2/P3 replaced by 1.00mm and 1.27mm headers - a 2-2.5x
pitch error on every one. Restoring upstream designators keeps
BUILD-DRAWING-REV04.PDF and the README BOM explainer applicable."
```

---

### Task 9: Trigger front-end, J3 replacement, and the ERC/netlist gate

**Files:**
- Modify: `hardware/rev2026/picoemp-rev2026.kicad_sch`
- Modify: `hardware/rev2026/tests/test_schematic.py`
- Create: `hardware/rev2026/tests/test_netlist.py`

**Interfaces:**
- Consumes: everything above.
- Produces: an ERC-clean schematic whose netlist differs from the baseline only in intended ways. Task 10 consumes this netlist.

- [ ] **Step 1: Write the failing tests**

Append to `hardware/rev2026/tests/test_schematic.py`:

```python
def test_trigger_front_end_present(syms):
    by_ref = {s.ref: s for s in syms}
    assert by_ref['U2'].value == '74LVC1G17'
    assert by_ref['R14'].value == '100R'
    assert by_ref['R15'].value == '10k'
    assert by_ref['C6'].value == '100n'

def test_bypass_resistor_is_dnp(syms):
    """R16 bypasses the buffer. Never fitted alongside U2."""
    r16 = next(s for s in syms if s.ref == 'R16')
    assert r16.value == '0R'
    assert r16.dnp, 'R16 must be DNP - fitting it with U2 causes output contention'

def test_optional_trigger_sma_is_dnp(syms):
    j4 = next(s for s in syms if s.ref == 'J4')
    assert j4.dnp, 'J4 is the optional trigger SMA and must be DNP'

def test_j3_is_wide_pitch(syms):
    """J3 carries ~500V. 2.54mm fails IEC 60664-1 creepage."""
    j3 = next(s for s in syms if s.ref == 'J3')
    assert j3.footprint, 'J3 has no footprint'
    assert '2.54mm' not in j3.footprint, 'J3 must not be 2.54mm pitch'
    assert any(p in j3.footprint for p in ('5.08mm', '5.0mm', '3.96mm')), \
        f'J3 footprint {j3.footprint!r} does not look like a wide-pitch connector'
```

Create `hardware/rev2026/tests/test_netlist.py`:

```python
import re
import subprocess

import pytest

import conftest

KC = '/Applications/KiCad/KiCad.app/Contents/MacOS/kicad-cli'

def test_erc_clean(tmp_path):
    report = tmp_path / 'erc.rpt'
    proc = subprocess.run(
        [KC, 'sch', 'erc', '--severity-error', '--exit-code-violations',
         '-o', str(report), str(conftest.SCH)],
        capture_output=True, text=True)
    assert proc.returncode == 0, f'ERC violations:\n{report.read_text()}'

def _nets(netlist_text):
    """Map net name -> set of 'REF.PIN' strings."""
    nets = {}
    for m in re.finditer(r'\(net \(code "[^"]*"\) \(name "([^"]*)"\)(.*?)\n    \)',
                         netlist_text, re.S):
        name, body = m.group(1), m.group(2)
        nodes = set(re.findall(r'\(node \(ref "([^"]+)"\) \(pin "([^"]+)"\)', body))
        nets[name] = {f'{r}.{p}' for r, p in nodes}
    return nets

def test_pico_pin_assignment_unchanged(tmp_path):
    """The firmware pin map must not drift. See spec section 2."""
    out = tmp_path / 'net.net'
    subprocess.run([KC, 'sch', 'export', 'netlist', '--format', 'kicadsexpr',
                    '-o', str(out), str(conftest.SCH)], check=True,
                   capture_output=True)
    nets = _nets(out.read_text())
    node_to_net = {n: name for name, nodes in nets.items() for n in nodes}

    # Pico physical pad -> net name fragment it must belong to.
    expected = {'U1.19': 'HVPULSE', 'U1.24': 'CHARGED',
                'U1.26': 'HVPWM', 'U1.31': 'CHARGED'}
    for node, frag in expected.items():
        assert node in node_to_net, f'{node} not connected'
        assert frag in node_to_net[node], \
            f'{node} on net {node_to_net[node]!r}, expected to contain {frag!r}'
```

- [ ] **Step 2: Run to verify they fail**

```bash
cd hardware/rev2026 && uv run --with pytest pytest tests/ -v
```

Expected: trigger/J3 tests fail (parts absent); ERC likely fails too.

- [ ] **Step 3: Draw the trigger front-end and swap J3**

In the Schematic Editor add:

```
P1.1 ──┬── R14 (100R) ──┬── U2 in            U2 (74LVC1G17)
       │                │                    pin 1 = OE/NC per package
J4 ────┘             R15 (10k)               pin 2 = A (in)
(DNP SMA)               │                    pin 4 = GND
                       GND                   pin 5 = VCC (+3V3)
                                             pin 3 = Y (out) ── GP0 (U1 pad 1)
C6 (100n) across U2 VCC/GND, placed at the part.
R16 (0R, DNP): trigger node ──── GP0
```

Check the 74LVC1G17 pinout against its datasheet before wiring — SOT-23-5 single-gate pinouts vary by vendor and the `74LVC1G17` GND/VCC assignment is not the same across all SOT-23-5 logic.

Disconnect GP0 from P1.1 directly; it now comes only from U2's output (or R16 if fitted).

Replace `J3`'s footprint with the selected 5.08 mm terminal block. Add a `BOM Comments` property on J3: `"HV calibration tap. Milled slot between pads - see spec section 7.3."`

Set `dnp` on `R16` and `J4`.

- [ ] **Step 4: Run to verify they pass**

```bash
cd hardware/rev2026 && uv run --with pytest pytest tests/ -v
```

Expected: all passed, including `test_erc_clean` and `test_pico_pin_assignment_unchanged`.

- [ ] **Step 5: Diff the netlist against the as-received design**

```bash
cd /Users/alex/Downloads/chipshouter-picoemp-main
KC=/Applications/KiCad/KiCad.app/Contents/MacOS/kicad-cli
$KC sch export netlist --format kicadsexpr -o /tmp/old.net hardware/altium_src/kc/ChipShouter-Pico.kicad_sch
$KC sch export netlist --format kicadsexpr -o /tmp/new.net hardware/rev2026/picoemp-rev2026.kicad_sch
diff <(grep -o '(name "[^"]*"' /tmp/old.net | sort -u) \
     <(grep -o '(name "[^"]*"' /tmp/new.net | sort -u)
```

Review every difference by hand. Each must be explainable as: the trigger front-end, the J3 change, or a designator rename. **Any unexplained net change means a symbol swap broke a connection — stop and fix it before continuing.**

- [ ] **Step 6: Commit**

```bash
git add hardware/rev2026
git commit -m "Add buffered trigger front-end, widen J3, gate on ERC and netlist parity

Trigger input gains a 74LVC1G17 Schmitt buffer (5.5V tolerant), series
and pulldown resistors, and a DNP bypass. J3 moves to 5.08mm: its
2.07mm pad gap failed IEC 60664-1 creepage at ~600V and the BG306's
500VAC rating is a proof test, not a working rating."
```

---

### Task 10: Board setup and HV layout ⚠️ HUMAN TASK

Layout is interactive. The steps below are for a person in KiCad's PCB editor; the tests are the acceptance gate.

**Files:**
- Create: `hardware/rev2026/picoemp-rev2026.kicad_pcb`
- Modify: `hardware/rev2026/picoemp-rev2026.kicad_pro`
- Create: `hardware/rev2026/tests/test_board.py`

**Interfaces:**
- Consumes: the ERC-clean schematic from Task 9.
- Produces: a board with the HV netclass configured and the HV section placed and routed.

- [ ] **Step 1: Measure the reference HV clearance**

The HV clearance rule is derived from the hi-pot-validated board, not invented.
This is a manual measurement — KiCad's **Inspect → Clearance Resolution** is the
authoritative tool and there is no scripted equivalent worth trusting for a
safety-relevant number.

Open `hardware/altium_src/kc/ChipShouter-Pico.kicad_pcb`. These are the legacy
net names on the HV rail, taken from that board's netlist:

```
NetC3_1   NetC3_2   NetD2_A   NetD4_K   NetD5_K   NetJ1_2   NetJ3_2
```

`NetC3_2` is the largest (53 pads) and is the main HV node.

For each of the three visually tightest spots where HV copper approaches
non-HV copper or a board edge: select the two items, run **Inspect → Clearance
Resolution**, and record the value. Take the **minimum** of the three.

Write that number down — it becomes `HV_CLEARANCE_MM` in Step 2 and the DRC rule
in Step 4.

- [ ] **Step 2: Write the failing test**

Create `hardware/rev2026/tests/test_board.py`, substituting the measured value for `HV_CLEARANCE_MM`:

```python
import json

import conftest

HV_CLEARANCE_MM = 0.0  # <-- replace with the value measured in Step 1

def _pro():
    return json.loads(conftest.PRO.read_text())

def test_min_clearance_is_enabled():
    """The port shipped with min_clearance = 0.0, i.e. DRC disabled."""
    rules = _pro()['board']['design_settings']['rules']
    assert rules['min_clearance'] > 0, 'min_clearance is 0 - DRC is not enforcing'

def test_hv_netclass_exists():
    classes = {c['name']: c for c in _pro()['net_settings']['classes']}
    assert 'HV' in classes, 'no HV netclass defined'

def test_hv_netclass_clearance():
    assert HV_CLEARANCE_MM > 0, 'measure the reference clearance first (Step 1)'
    classes = {c['name']: c for c in _pro()['net_settings']['classes']}
    assert classes['HV']['clearance'] >= HV_CLEARANCE_MM, \
        'HV clearance is looser than the hi-pot-validated reference board'

def test_hv_netclass_has_members():
    settings = _pro()['net_settings']
    patterns = json.dumps(settings)
    for net in ('HVPULSE',):
        assert net in patterns or 'HV' in patterns
```

- [ ] **Step 3: Run to verify it fails**

```bash
cd hardware/rev2026 && uv run --with pytest pytest tests/test_board.py -v
```

Expected: failures — no `.kicad_pcb`, no HV class, `min_clearance` is 0.

- [ ] **Step 4: Configure the board in KiCad**

File → Board Setup:

- **Board thickness 1.6 mm.** The edge-mount SMA is specified for 0.062″ board and clamps the edge.
- Copper layers: 2.
- Constraints: set `min_clearance` to 0.2 mm (was 0.0 — DRC was not enforcing).
- Net classes: add `HV` with clearance = the Step 1 measurement. Assign the HV rail nets: the T1 secondary, D2 anode/cathode, C3 both nodes, Q2 collector, J1 centre pin, R1's high side, and J3.
- Import the outline: copy `Edge.Cuts` from `hardware/altium_src/kc/ChipShouter-Pico.kicad_pcb` (40 × 116 mm with its slots and arcs).

- [ ] **Step 5: Place and route the HV section**

Update PCB from Schematic. Then replicate placement and copper for `T1, T2, C1, C2, C3, D2, D3, D4, D5, Q1, Q2, R1, R2, J3` from the legacy board — open it side by side and match positions. This geometry is what was hi-pot tested at 1 kV.

Confirm the T1/T2 pin-1 dot orientation matches `hardware/BUILD-DRAWING-REV04.PDF`.

- [ ] **Step 6: Run to verify it passes**

```bash
cd hardware/rev2026 && uv run --with pytest pytest tests/test_board.py -v
```

Expected: all passed.

- [ ] **Step 7: Commit**

```bash
git add hardware/rev2026
git commit -m "Board setup with HV netclass, HV section placed and routed

min_clearance was 0.0 in the port, meaning DRC enforced nothing on a
board that generates ~500V. HV clearance is derived from measuring the
hi-pot-validated reference layout rather than chosen arbitrarily."
```

---

### Task 11: Logic layout, J3 creepage slot, DRC gate ⚠️ HUMAN TASK

**Files:**
- Modify: `hardware/rev2026/picoemp-rev2026.kicad_pcb`
- Modify: `hardware/rev2026/tests/test_board.py`

**Interfaces:**
- Consumes: Task 10's board.
- Produces: a fully routed, DRC-clean board ready for fab output.

- [ ] **Step 1: Write the failing test**

Append to `hardware/rev2026/tests/test_board.py`:

```python
import subprocess

KC = '/Applications/KiCad/KiCad.app/Contents/MacOS/kicad-cli'

def test_drc_clean_with_schematic_parity(tmp_path):
    report = tmp_path / 'drc.rpt'
    proc = subprocess.run(
        [KC, 'pcb', 'drc', '--severity-error', '--schematic-parity',
         '--exit-code-violations', '-o', str(report), str(conftest.PCB)],
        capture_output=True, text=True)
    assert proc.returncode == 0, f'DRC violations:\n{report.read_text()}'

def test_board_outline_is_40x116mm():
    import kicad_parse as kp
    pcb = kp.parse_file(conftest.PCB)
    xs, ys = [], []
    for node in kp._walk(pcb, 'gr_line'):
        layer = next((c for c in node if isinstance(c, list) and c and c[0] == 'layer'), None)
        if not layer or kp.sval(layer[1]) != 'Edge.Cuts':
            continue
        for tag in ('start', 'end'):
            pt = next((c for c in node if isinstance(c, list) and c and c[0] == tag), None)
            if pt:
                xs.append(float(pt[1])); ys.append(float(pt[2]))
    assert xs, 'no Edge.Cuts geometry found'
    w, h = max(xs) - min(xs), max(ys) - min(ys)
    assert abs(w - 40.0) < 0.5, f'board width {w:.2f} mm, expected 40'
    assert abs(h - 116.0) < 0.5, f'board height {h:.2f} mm, expected 116'
```

- [ ] **Step 2: Run to verify it fails**

```bash
cd hardware/rev2026 && uv run --with pytest pytest tests/test_board.py -v
```

Expected: DRC fails on unrouted nets.

- [ ] **Step 3: Place and route the logic side**

Place U1 (Pico), U2, D6/D8/D9, SW1–SW3, P1–P3, R5, R10–R16, C5, C6, D1, J2, MH1–MH3, FID1–FID3. Route freely — this side has no special constraints beyond the default 0.2 mm class.

Keep the trigger path (P1.1 → R14 → U2 → GP0) short and away from the HV section.

- [ ] **Step 4: Confirm JLCPCB fab limits, then add the J3 creepage slot**

Invoke the `kicad-happy:jlcpcb` skill for the current 2-layer capability set —
minimum trace/space, hole size, annular ring — and check the board against it.

The skill does **not** document minimum routed slot width, so check JLCPCB's live
capabilities page for that specific number before committing the slot geometry.
It is router-bit limited, typically around 1.0 mm.

Draw the slot on `Edge.Cuts` between J3's two HV pads.

If the slot proves impractical, the documented fallback is wider pad separation
plus conformal coating.

- [ ] **Step 5: Run to verify it passes**

```bash
cd hardware/rev2026 && uv run --with pytest pytest tests/ -v
```

Expected: everything passes, including DRC with schematic parity.

- [ ] **Step 6: Visual and mechanical review**

Open the 3D viewer. Verify:
- Switch actuators clear the 1551B half-shell.
- Nothing collides with the shield footprint.
- The Pico sits flat with clearance for SW1/SW2 (upstream: fit those *after* the module).

- [ ] **Step 7: Commit**

```bash
git add hardware/rev2026
git commit -m "Route logic side, add J3 creepage slot, DRC clean with schematic parity"
```

---

### Task 12: Fab outputs and DigiKey BOM

**Files:**
- Create: `hardware/rev2026/tools/export.sh`
- Create: `hardware/rev2026/BUILD-NOTES.md`

**Interfaces:**
- Consumes: the DRC-clean board from Task 11.
- Produces: gerbers + drill in `out/`, a cart-ready DigiKey CSV, and a change note.

- [ ] **Step 1: Write the export script**

Create `hardware/rev2026/tools/export.sh`:

```bash
#!/usr/bin/env bash
set -euo pipefail
KC=/Applications/KiCad/KiCad.app/Contents/MacOS/kicad-cli
HERE="$(cd "$(dirname "$0")/.." && pwd)"
SCH="$HERE/picoemp-rev2026.kicad_sch"
PCB="$HERE/picoemp-rev2026.kicad_pcb"
OUT="$HERE/out"
mkdir -p "$OUT/gerbers"

SK=/Users/alex/.claude/plugins/cache/kicad-happy/kicad-happy/2.0.0/skills

"$KC" pcb export gerbers --output "$OUT/gerbers/" "$PCB"
"$KC" pcb export drill   --output "$OUT/gerbers/" "$PCB"
(cd "$OUT/gerbers" && zip -qr ../picoemp-rev2026-gerbers.zip .)

"$KC" sch export pdf -o "$OUT/picoemp-rev2026-sch.pdf" "$SCH"

# BOM tracking CSV and DigiKey order file via the kicad-happy bom skill.
mkdir -p "$HERE/bom"
uv run python "$SK/bom/scripts/bom_manager.py" export "$SCH" \
  -o "$HERE/bom/bom.csv" --recursive
uv run python "$SK/bom/scripts/bom_manager.py" order "$HERE/bom/bom.csv" \
  -o "$OUT/orders/" --distributor digikey --boards 5 --spares 2

echo "Outputs in $OUT"
```

- [ ] **Step 2: Run it**

```bash
chmod +x hardware/rev2026/tools/export.sh && hardware/rev2026/tools/export.sh
```

Expected: `out/picoemp-rev2026-gerbers.zip`, `out/picoemp-rev2026-sch.pdf`,
`bom/bom.csv`, and `out/orders/digikey.csv`.

The `--boards 5 --spares 2` gives five boards plus two spares per line — right for
hand assembly, where you will lose a few 0603s to the carpet.

- [ ] **Step 3: Verify the BOM**

```bash
column -s, -t hardware/rev2026/bom/bom.csv | less -S
```

Check: every line has an MPN; DNP parts (R16, J4) are excluded from the order; the
four forced changes are present — `APT1608SURCK` on D6/D9, `RC0805FR-072KL` on R9,
the wide-pitch J3, and the U2/R14/R15/C6 front-end.

Add the NRND lifetime-buy quantities to the order file by hand: **30 ×
ATB322524-0110-T000** and **10 × RGT16BM65DTL**, overriding the calculated
quantities. Neither has a successor and the transformer has no equivalent from any
vendor.

Also append the off-board items from spec §5.2c — battery holder, probe SMA, probe
inductor, ferrite, USB isolator. They are not on the schematic and the exporter
cannot know about them.

- [ ] **Step 3b: Validate part numbers against DigiKey**

Only if `DIGIKEY_CLIENT_ID` and `DIGIKEY_CLIENT_SECRET` are configured. Invoke
`kicad-happy:digikey` and verify each PN resolves and is in stock — distributor
part numbers go stale, and the upstream BOM is from 2022.

If credentials are not set, skip this and validate by pasting the order CSV into
DigiKey's web cart, which reports unrecognised part numbers directly. Note in the
commit message which route was used.

- [ ] **Step 4: Write the build note**

Create `hardware/rev2026/BUILD-NOTES.md` documenting, at minimum: the four BOM changes with reasons, the NRND lifetime-buy guidance (30 × ATB322524, 10 × RGT16BM65DTL), the hand-solder list (J1 SMA, J2 JST, J3 terminal block, P1–P3), and the staged bring-up procedure from spec section 9. Attribute NewAE Technology and note CC BY-SA 3.0.

- [ ] **Step 5: Review the gerbers before ordering**

Open `out/gerbers/` in KiCad's Gerber Viewer. Confirm the board outline, the J3 slot, and the drill file. **Do not order without this check.**

- [ ] **Step 6: Commit**

```bash
git add hardware/rev2026
git commit -m "Add fab export script, DigiKey BOM, and build notes"
```

---

### Task 13: Full design review before ordering

The last gate. ERC and DRC prove the design is *internally consistent*; they do not
prove it is *correct*. This task looks for the class of problem the original audit
found — wrong part for the job, missing decoupling, power-path mistakes.

**Files:**
- Create: `hardware/rev2026/DESIGN-REVIEW.md`

**Interfaces:**
- Consumes: the complete design from Task 12.
- Produces: a written review with every finding either fixed or explicitly accepted.

- [ ] **Step 1: Run the kicad skill's design review**

Invoke `kicad-happy:kicad` and ask it to review `hardware/rev2026/` — schematic,
board, footprints, power tree, and DFM. Point it at the spec so it knows what was
intentional.

Ask specifically about:
- The trigger front-end: is the 74LVC1G17 pinout wired correctly for its package?
  Single-gate SOT-23-5 logic has vendor-specific VCC/GND assignments and this is
  new circuitry with no upstream reference.
- Decoupling: does every powered part have a local cap? U2 is new.
- The HV creepage geometry around J3 and the slot.
- Whether the D7 clamp still sits directly across the IGBT gate with the shortest
  possible loop — upstream warns a reversed or open D7 destroys Q2.

- [ ] **Step 2: Cross-check against the original audit**

Re-read `hardware/altium_src/kc/audit/AUDIT.md` §1–§3 and confirm every blocking
issue is resolved in the new design:

| Audit finding | Must now be |
|---|---|
| 20 duplicated footprints | Board built fresh from the schematic — none possible |
| Split netlist, copper on legacy nets | Single netlist, DRC schematic-parity clean |
| Five header footprints at wrong pitch | P1/P2/P3 at 2.54 mm (Task 8 test) |
| 26 unregistered libraries | Project-local tables (Task 2 test) |
| Eight symbols with no footprint | All assigned (Task 7 test) |
| Wrong symbol classes | Corrected (Task 5 tests) |
| R9 part-number bug | Fixed (Task 3 test) |
| C5 literal `${ALTIUM_VALUE}` | Fixed (Task 3 test) |
| `min_clearance` = 0.0 | Enforced (Task 10 test) |
| No HV netclass | Defined and measured (Task 10 test) |

- [ ] **Step 3: Write the review document**

Create `hardware/rev2026/DESIGN-REVIEW.md`. For each finding record: what it is,
severity, and either the fix commit or an explicit written rationale for accepting
it. **An unresolved finding blocks ordering.**

- [ ] **Step 4: Run the full test suite one final time**

```bash
cd hardware/rev2026 && uv run --with pytest pytest tests/ -v
```

Expected: everything passes.

- [ ] **Step 5: Commit**

```bash
git add hardware/rev2026
git commit -m "Add pre-fabrication design review"
```

---

## Self-Review

**Spec coverage.** Every spec section maps to a task: §5.1 forced changes → Tasks 3, 9, 11; §5.2/5.2b/5.2c/5.3 BOM → Task 12; §5.4 NRND lifetime buy → Task 12 Step 3; §6.1 libraries → Tasks 2, 6, 7; §6.2 symbols → Tasks 4, 5; §6.3 fields → Task 3; §6.4 trigger → Task 9; §6.5 designators → Task 8; §7.1 board setup → Task 10; §7.2 netclasses → Task 10; §7.3 slot → Task 11; §7.4 HV replication → Task 10; §8 gates → Tasks 9, 11, 13; §10 open items → Tasks 6 and 8; §12 licensing → Task 12 Step 4; §13 deliverables → Task 12.

**Resolved during execution, by design:**
- Switch part numbers and actuator heights (spec §10) — Task 8 Step 3, after a physical measurement against the shield. The plan cannot supply them.
- HV clearance value — measured in Task 10 Step 1.
- J3 terminal block MPN — selected in Task 9 Step 3. The plan constrains pitch, not vendor.
- D7 SOD-323 vs SOD-323F, and SOD-123F vs FL — Task 6 Step 5, from datasheets.
- JLCPCB minimum routed slot width — Task 11 Step 4, from their live capability page.

**Out of scope:** spec §9 bring-up is post-fabrication.

**DigiKey API is optional and currently unconfigured.** Every step that could use it has a no-auth fallback (element14 or LCSC for datasheets, DigiKey's web cart for part validation). Task 12 Step 3b is the only step gated on it, and it is explicitly skippable. Do not block on credentials.

**Type consistency.** `kicad_parse` exports `parse`, `parse_file`, `sval`, `_walk`, `symbols`, `footprints`, `ref_key`, `Symbol`, `Footprint`. `Symbol` fields (`ref`, `value`, `lib_id`, `footprint`, `props`, `in_bom`, `dnp`) are used consistently in Tasks 1, 3, 5, 7, 8, 9. `Footprint` fields (`ref`, `lib_id`, `value`, `pads`) are used in Task 6 and Task 11. `conftest` exports `ROOT`, `SCH`, `PCB`, `PRO` and fixtures `root`, `sch`, `syms` — used consistently throughout.
